SalihAyvaci21/AC-DC-G-Kayna-/AC-DC Güç kaynağı/Images/3D Images.PNG

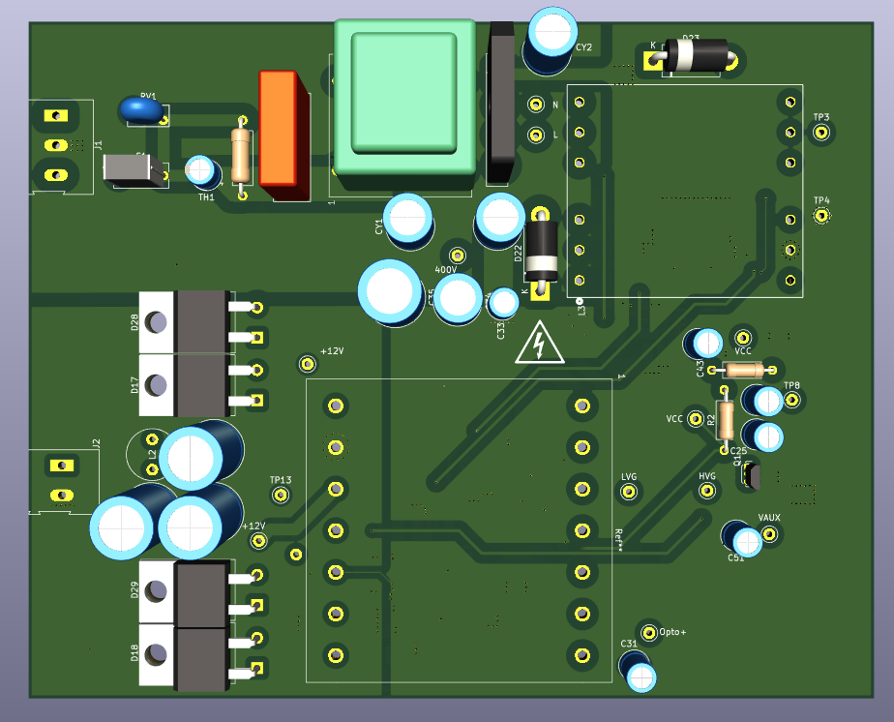
AC-DC Güç kaynağı/Images/3D Images.PNG
