SalihAyvaci21/AC-DC-G-Kayna-/AC-DC Güç kaynağı/Images/PFC_Transformer_Coil.PNG

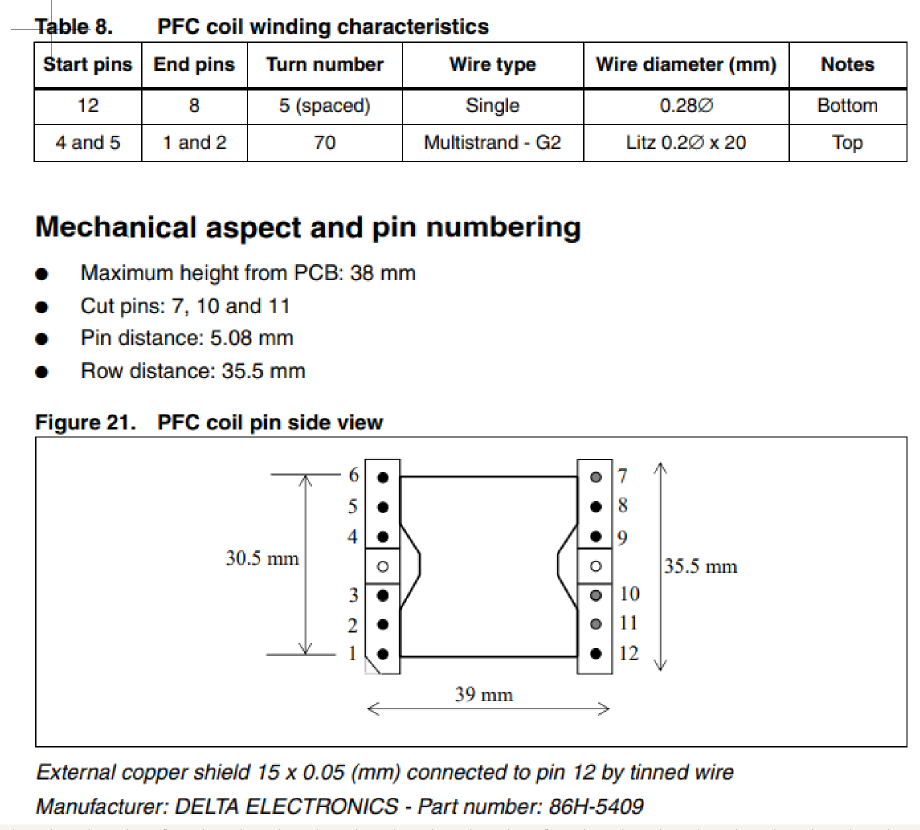
AC-DC Güç kaynağı/Images/PFC_Transformer_Coil.PNG
